mechatronicmagic/farseer-pcb/documentation/filter/high-pass-filter-design.png

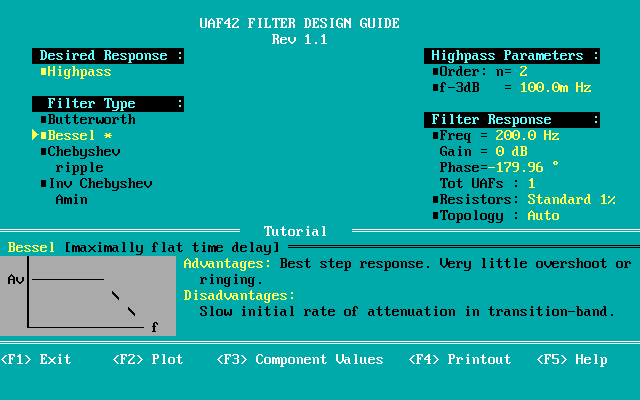
documentation/filter/high-pass-filter-design.png
