mechatronicmagic/farseer-pcb/documentation/filter/high-pass-filter-plot.png

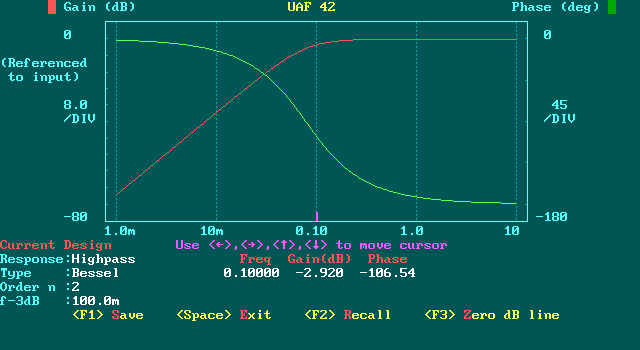
documentation/filter/high-pass-filter-plot.png
