mechatronicmagic/farseer-pcb/documentation/filter/high-pass-filter-components.png

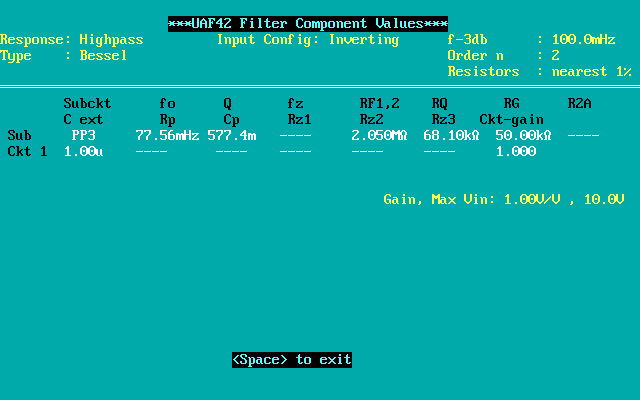
documentation/filter/high-pass-filter-components.png
