mechatronicmagic/farseer-pcb/documentation/3dmodels/step/tube-lens-nut.step

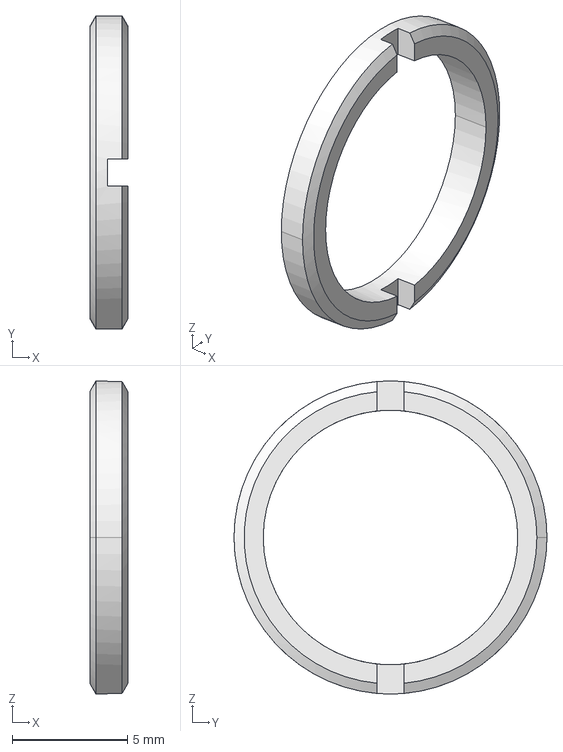
[picture p29: CAD file, 2025-05-16]
documentation/3dmodels/step/tube-lens-nut.step
1.65 x 13.6 x 13.6 mm
