mechatronicmagic/farseer-pcb/documentation/assembly/assembly0.png

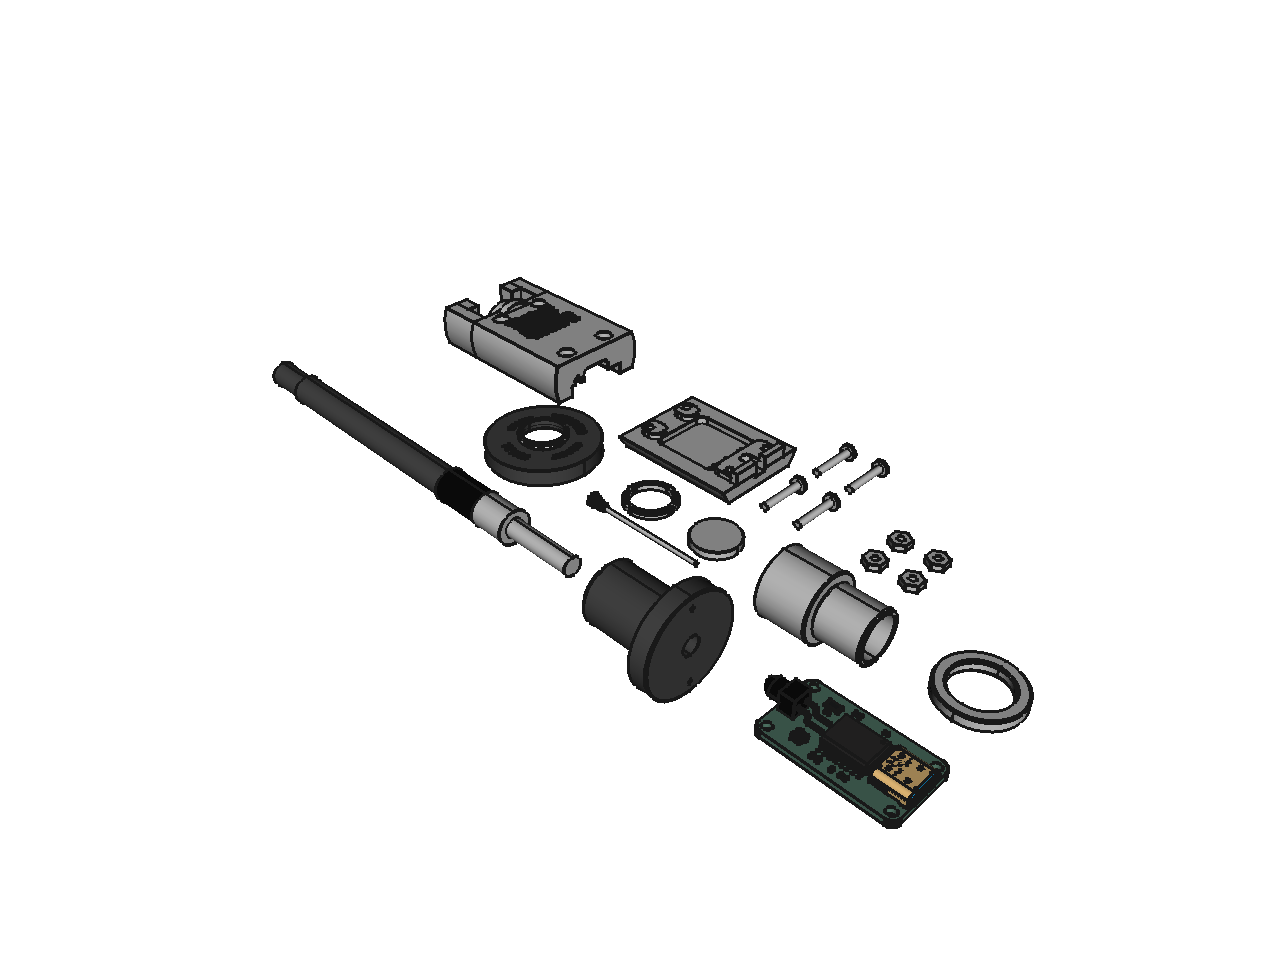
documentation/assembly/assembly0.png
